MOSH-Insa-Toulouse/2021-2022---TOURNIER-NAVARRO-Projet-Capteur/LTspice/Circuit avec capteur.asc

C1: cap; 100n
C2: cap; 100n
C4: cap; 1µ
C5: cap; 1p
R1: res; 100k
R2: res; 1k
R3: res; 100k
R5: res; 10k
R6: res; 1k
U1: LTC1050
V1: voltage; 5
V2: voltage; SINE(0 325 50)
V3: voltage; SINE(0 1 0.2 0.1 0.1 10); AC 1 0
X1: GP_Capteur_Graphite
Named nets: 0, ADC, Vemp, Vep
;tran 12
.ac dec 100 1 1G
.param G0 10n
.param R0 1k
.param C0 200p
