MOSH-Insa-Toulouse/2021-2022---TOURNIER-NAVARRO-Projet-Capteur/LTspice/GP_Capteur_Graphite.asc

B1: bi; I=V(cp,cn)*({G0}+v(gc,gn)*{G0})
C1: cap; {C0}
R1: res; {R0}
Named nets: gp, gn, gc, cp, cn
